t0lkim/the-stream-deck/code/streamdeck-vu-driver.kicad_sch

## KiCad design code/streamdeck-vu-driver.kicad_sch (2026-04-05, last stored version)

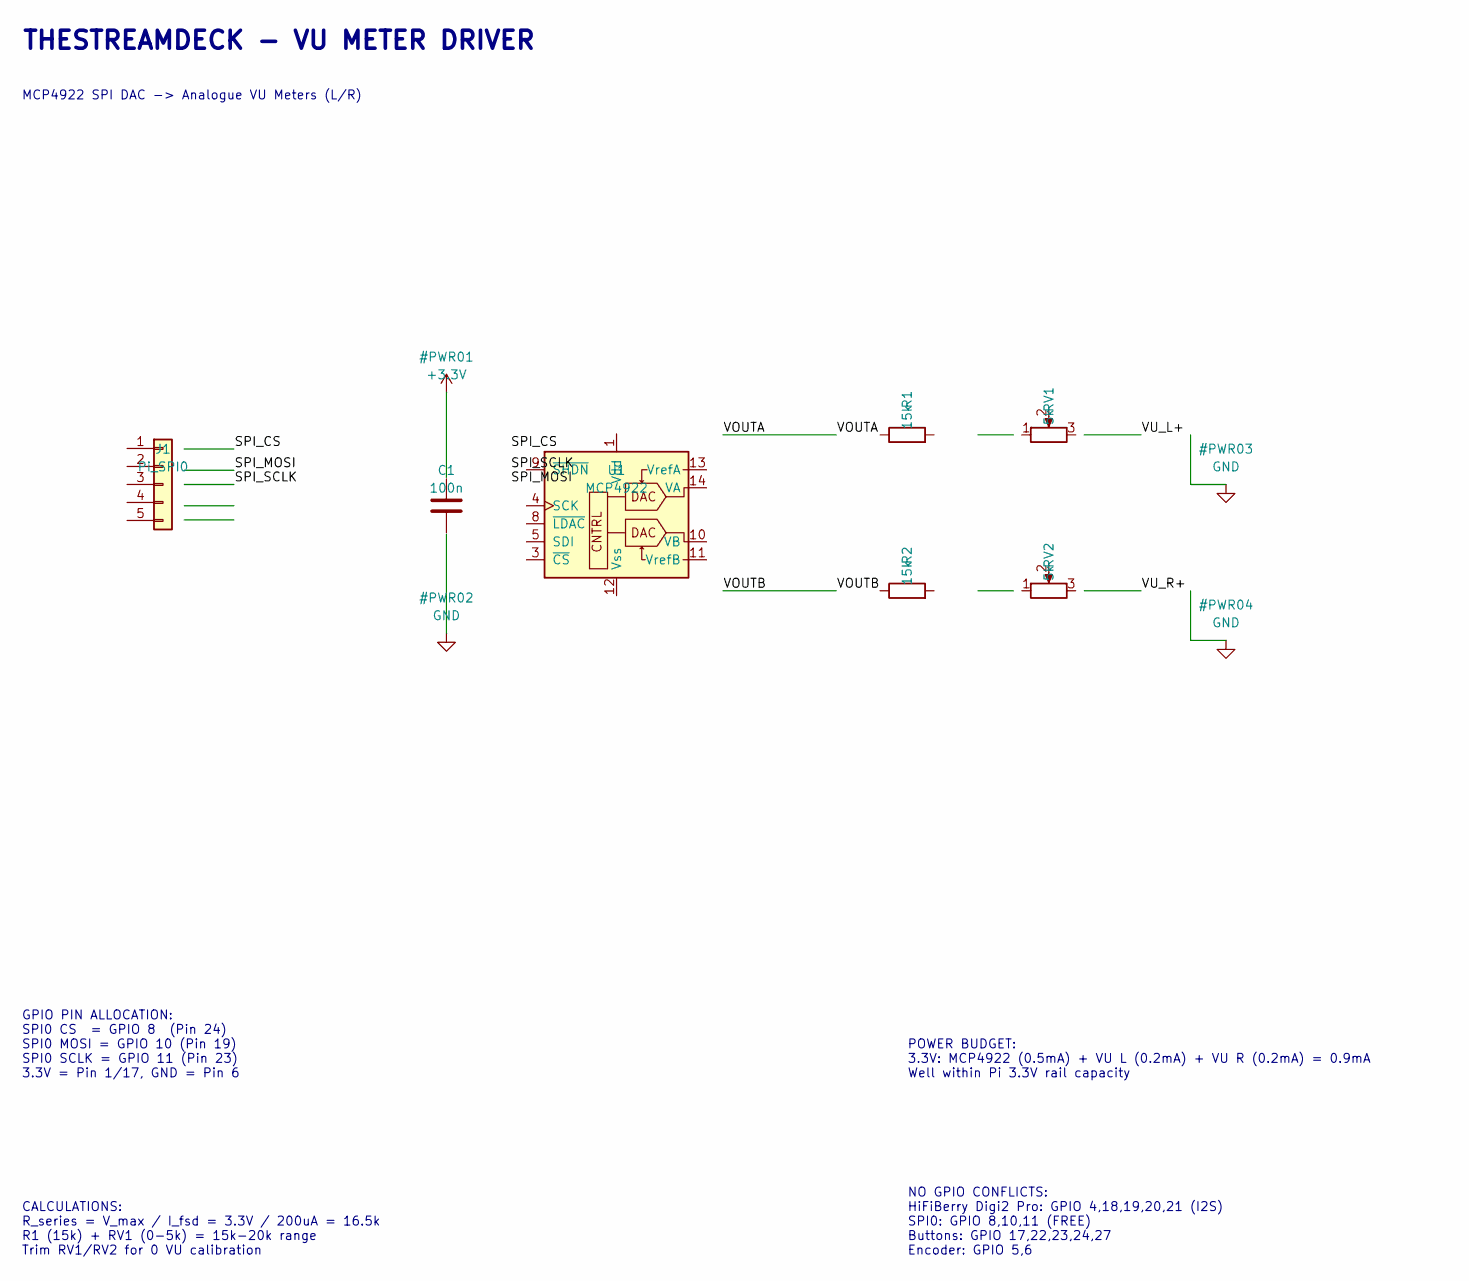
[picture p9: schematic streamdeck-vu-driver.kicad_sch]

Parts:
C1: 100n
J1: Pi_SPI0
R1, R2: 15k
RV1, RV2: 5k
U1: MCP4922; DIP-14_W7.62mm

Notes on the sheet:
THESTREAMDECK - VU METER DRIVER
MCP4922 SPI DAC -> Analogue VU Meters (L/R)
GPIO PIN ALLOCATION: SPI0 CS = GPIO 8 (Pin 24) SPI0 MOSI = GPIO 10 (Pin 19) SPI0 SCLK = GPIO 11 (Pin 23) 3.3V = Pin 1/17, GND = Pin 6
CALCULATIONS: R_series = V_max / I_fsd = 3.3V / 200uA = 16.5k R1 (15k) + RV1 (0-5k) = 15k-20k range Trim RV1/RV2 for 0 VU calibration
POWER BUDGET: 3.3V: MCP4922 (0.5mA) + VU L (0.2mA) + VU R (0.2mA) = 0.9mA Well within Pi 3.3V rail capacity
NO GPIO CONFLICTS: HiFiBerry Digi2 Pro: GPIO 4,18,19,20,21 (I2S) SPI0: GPIO 8,10,11 (FREE) Buttons: GPIO 17,22,23,24,27 Encoder: GPIO 5,6
